danieltyukov/tud-micro-led-bonding-categorization/docs/Work with Ahmed.md

1. design of the PCB for the characterization of the led.
2. practically in the clean-room solder printing placing the led dies pick and places tool and placing it on the PCB, with the existing PCB or with the shipped new PCB from the design.
3. geometric characterization of the led dies, with 3d scans, bond line thickness and die tilt. Alignment after bonding (not expected).
4. measurement and characterization. when fully assembly.
