danieltyukov/tud-micro-led-bonding-categorization/deliverable/for_ahmed_2026-08-12/figures/daisy_chain_resistance.pdf

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
ditio

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
Total chain resistance (+)

0.2 0.3 0.4 0.5 0.6
