danieltyukov/tud-micro-led-bonding-categorization/deliverable/for_ahmed_2026-08-12/figures/daisy_chain_resistance.png

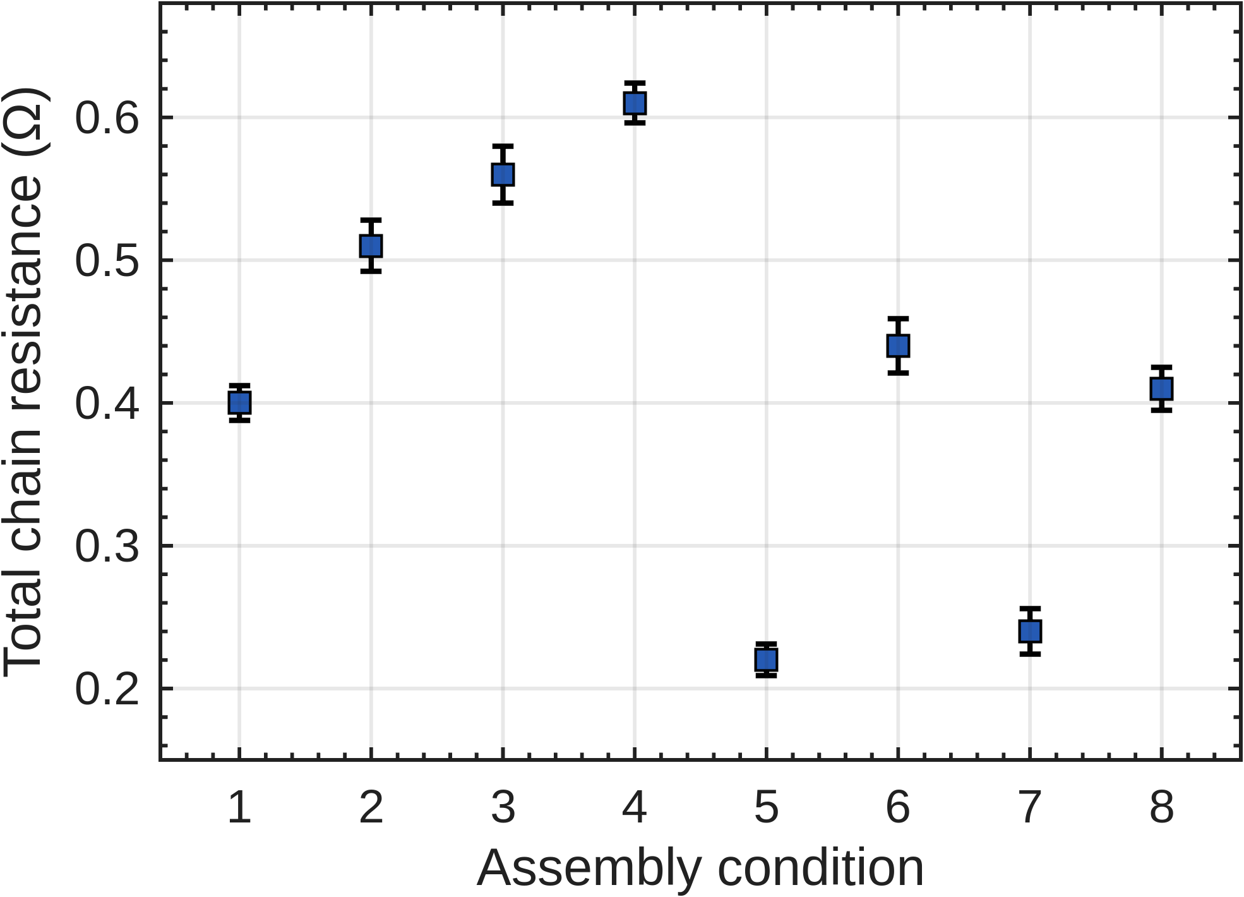
deliverable/for_ahmed_2026-08-12/figures/daisy_chain_resistance.png
