danieltyukov/tud-micro-led-bonding-categorization/deliverable/for_ahmed_2026-10-10/figures/die_shear_strength_bars.png

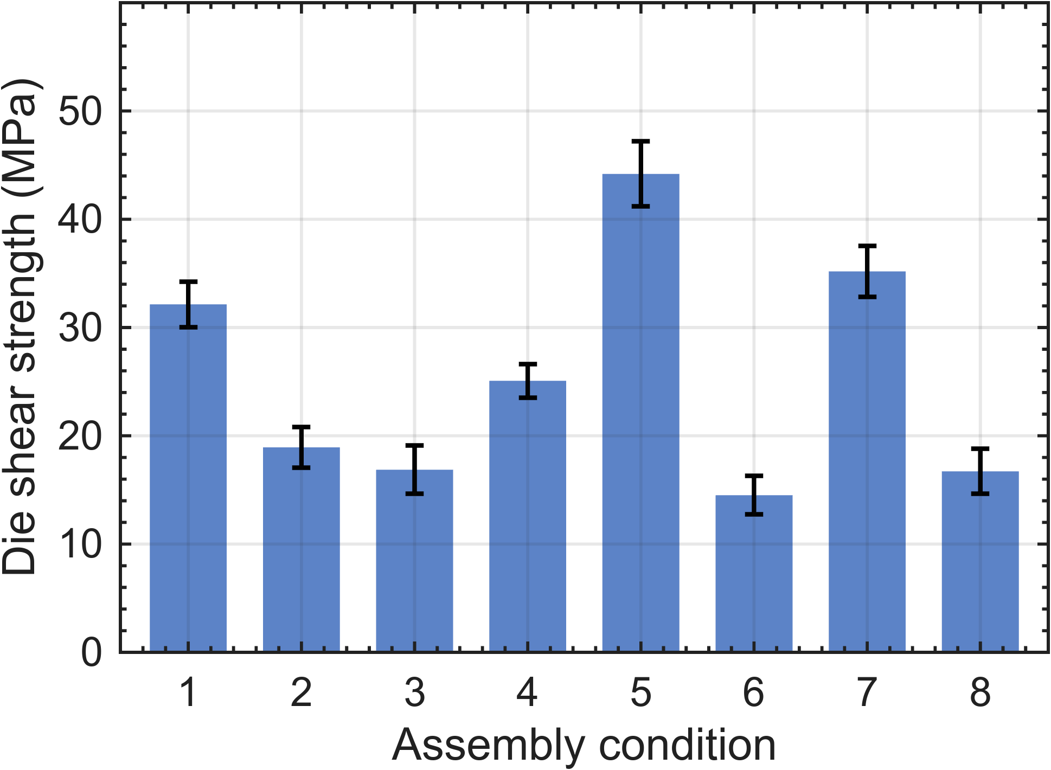
deliverable/for_ahmed_2026-10-10/figures/die_shear_strength_bars.png
