danieltyukov/tud-micro-led-bonding-categorization/new-pcb/fab/stencil-v2/paste_preview.png

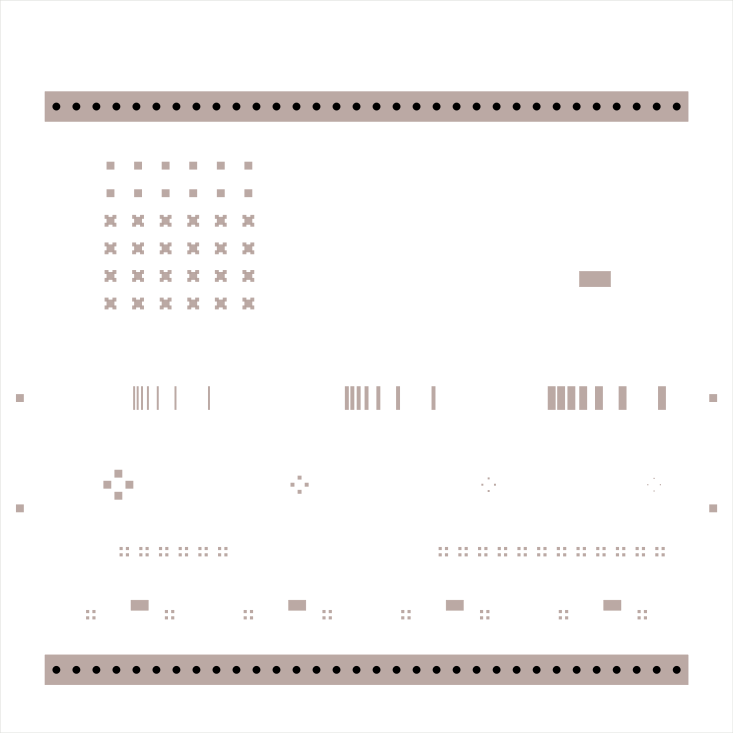
new-pcb/fab/stencil-v2/paste_preview.png
