danieltyukov/tud-micro-led-bonding-categorization/part2/photos-during-lab2/20260522_151641.jpg

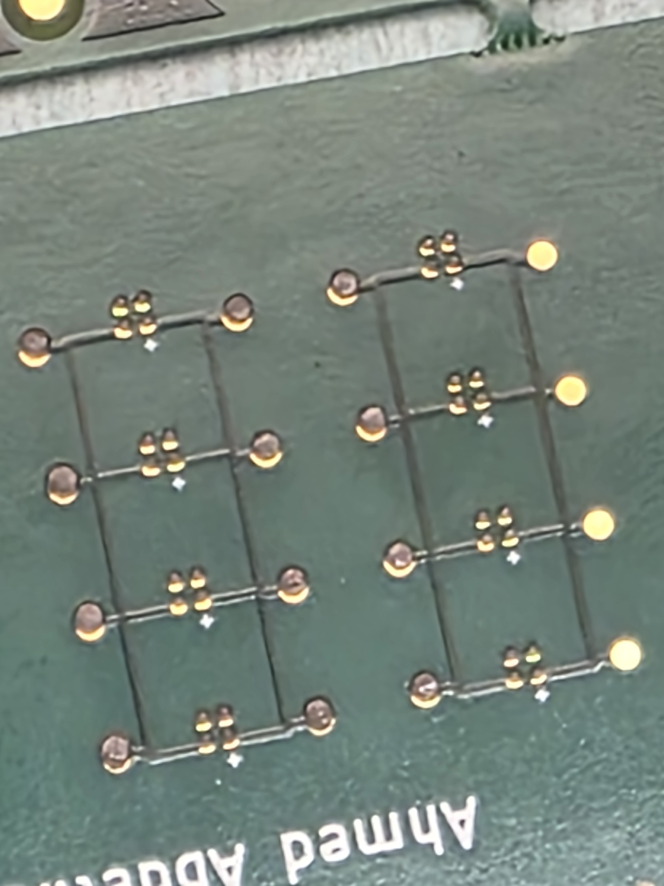
part2/photos-during-lab2/20260522_151641.jpg
