danieltyukov/tud-micro-led-bonding-categorization/part2/photos-during-lab2/20260522_152103.jpg

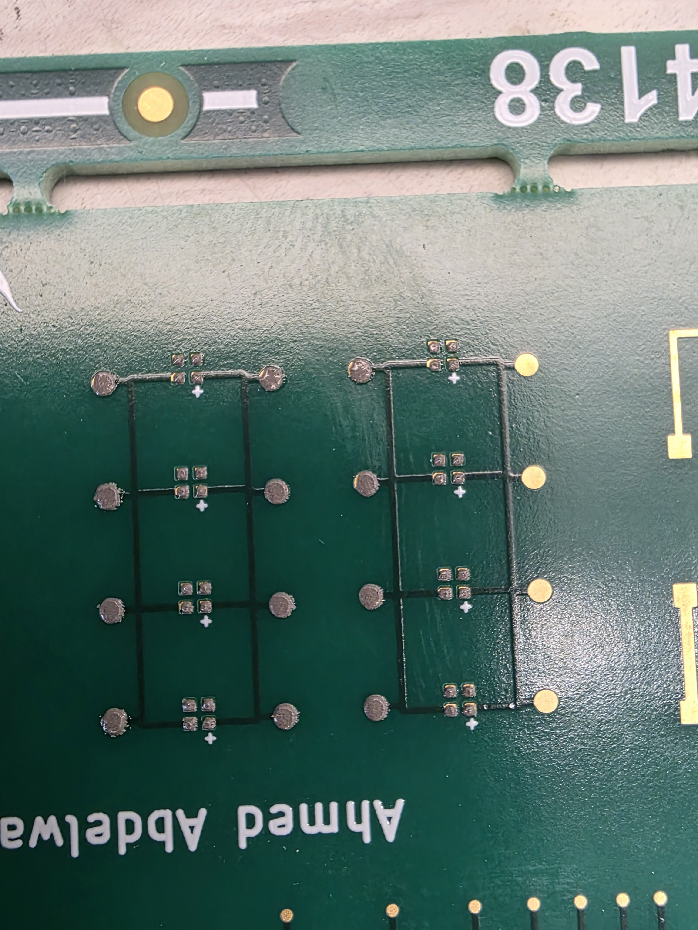
part2/photos-during-lab2/20260522_152103.jpg
