danieltyukov/tud-micro-led-bonding-categorization/report/figures/schematic.png

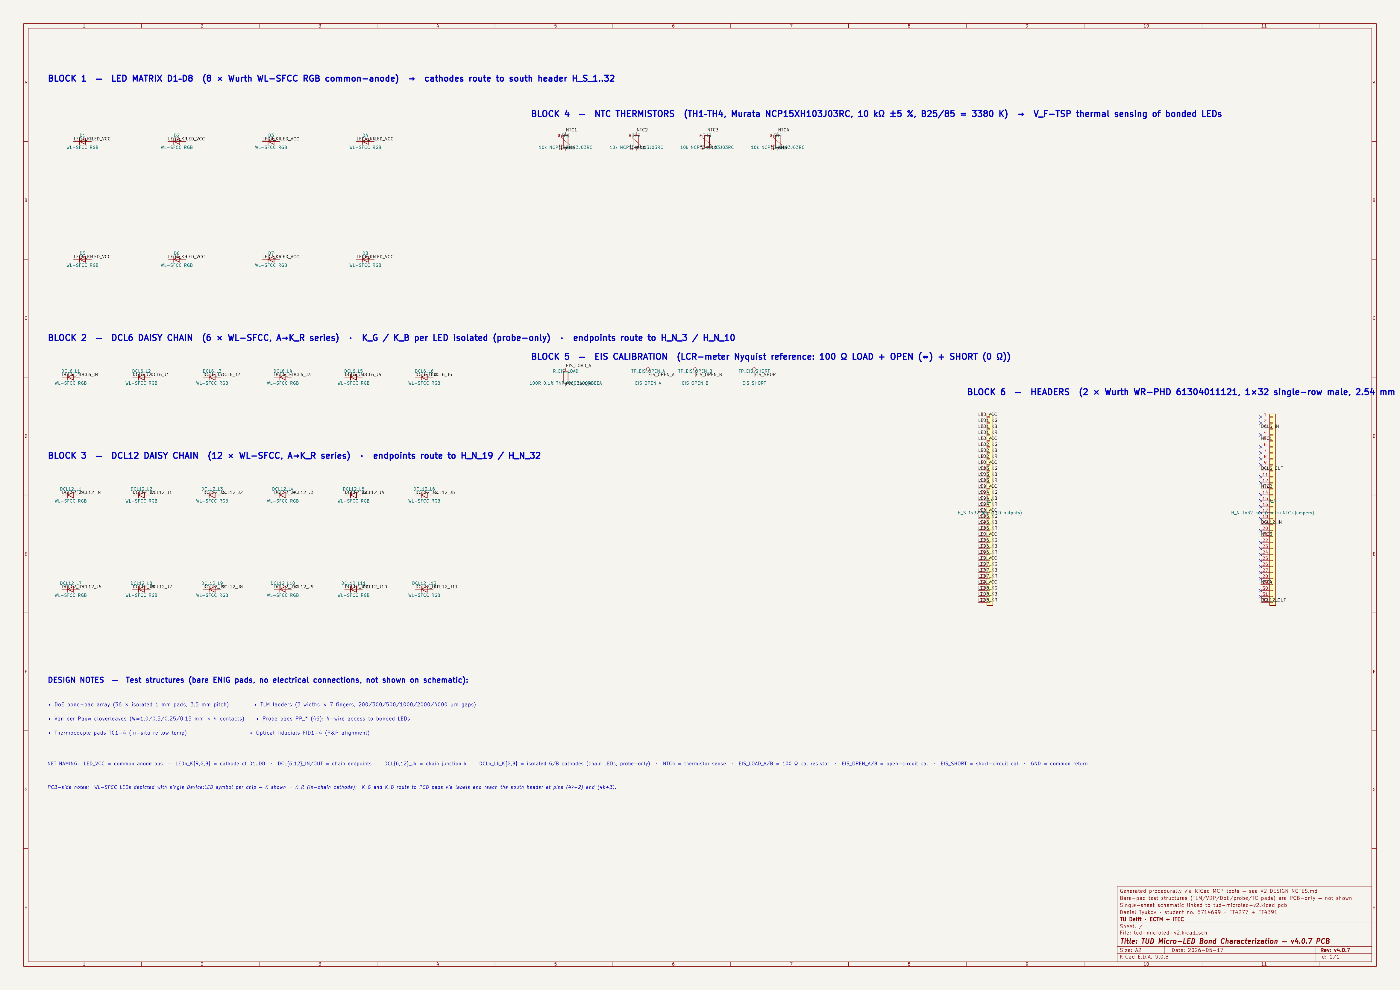
report/figures/schematic.png
