danieltyukov/tud-micro-led-bonding-categorization/RESULTS/R1_photos/2026-08-03_board1_overview.jpg

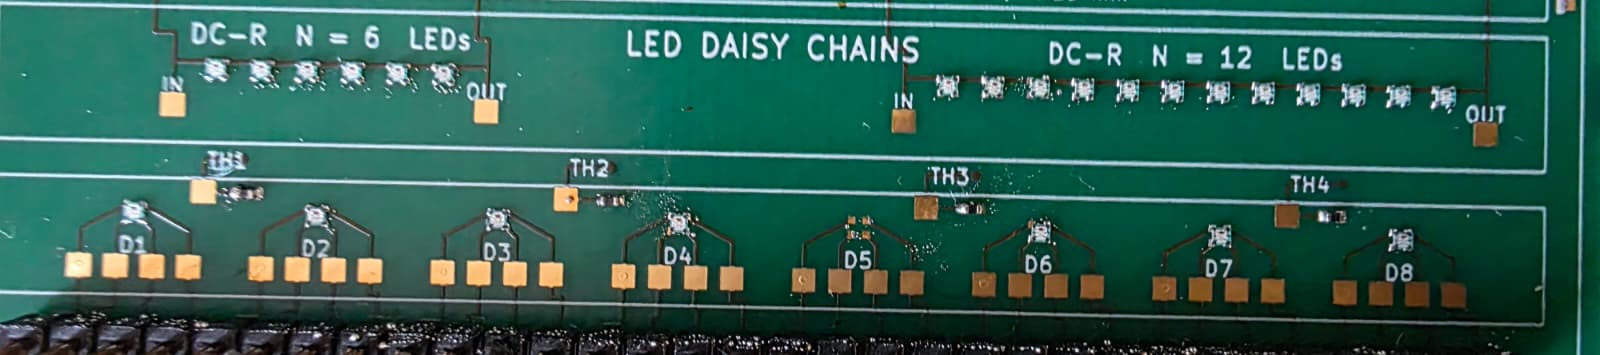
RESULTS/R1_photos/2026-08-03_board1_overview.jpg
