danieltyukov/tud-micro-led-bonding-categorization/RESULTS/R1_photos/2026-08-03_board2_overview.jpg

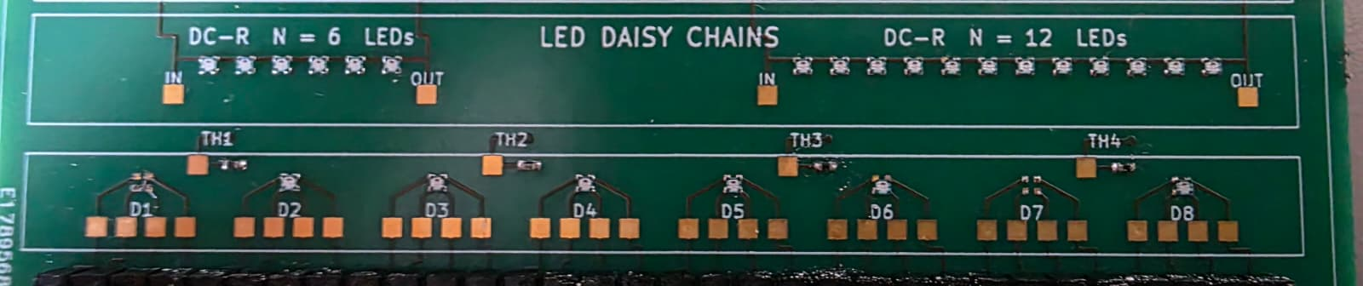
RESULTS/R1_photos/2026-08-03_board2_overview.jpg
