danieltyukov/tud-micro-led-bonding-categorization/RESULTS/R1_photos/2026-08-03_board7-8_overview.jpg

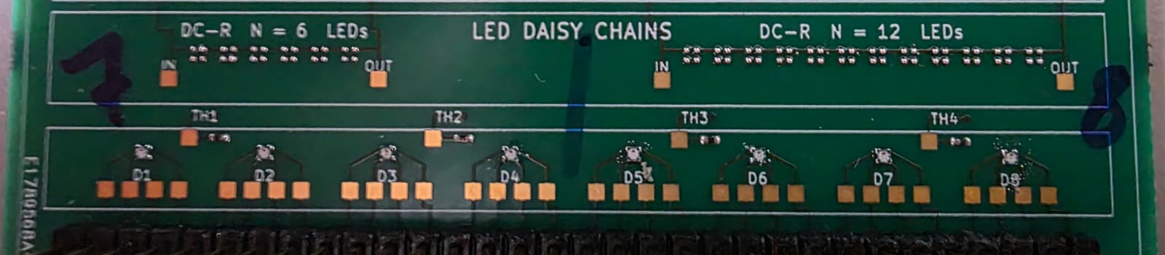
RESULTS/R1_photos/2026-08-03_board7-8_overview.jpg
