danieltyukov/tud-micro-led-bonding-categorization/deliverable/microLED_electrical_characterization/firmware/reverse_bias_wiring.pdf

Step 6 - reverse leakage. Rewire from the sweep rig.

The bank comes off, the die is driven BACKWARDS, and the meter reads ACROSS THE DIE. Healthy reads near 5 V; a shunt pulls it down.

J | J
I | I
H | H
G | G
F | F
E | E
D | D
C | C
B | B
A | A
1 | 5 | 10 | 15 | 20 | 25 | 30

top half + both top rails: leave empty rail holes: first at col 3, then five, a one-hole gap, five, ...

FORCE

GND
FORCE

GND

ATmega328P

## ARDUINO UNO

SCLSDAARFGND 13 12 11 10 9 | 8 | 7 | 6 | 5 | 4 | 3 | 2 | 1 | 0
NC IOR RST3V3 5V GNDGNDVIN | A0 A1 A2 A3 A4 A5

DIGITAL

POWER | ANALOG IN

### your PCB - SOUTH 32-pin header

pins 1-4 = D1, 5-8 = D2, ... 29-32 = D8

KR

1

A KG KB KR

5

A KG KB KR

9

A KG KB KR

13

A KG KB KR

17

A KG KB KR

21

A KG KB KR

25

A KG KB KR

29

A KG KB

32

D1 | D2 | D3 | D4 | D5 | D6 | D7 | D8
die Dn: anode = pin 4n-2 red K = 4n-3 green K = 4n-1 blue K = 4n

REMOVE these six D2-D7 jumpers - that kills the bank everything faded stays on the board, it is simply not used

100 k, measured 98.0 k

GND rail col 28

RED probe - J14

BLACK probe
any GND rail hole

the meter goes across the DIE, not across the resistor

## the rewire, in five moves

1 PULL the six jumpers off UNO D2-D7. Bank is dead.

2 ADD a jumper: UNO 5V -> G10.

3 ADD the 100 k across the top half: F10 to F14.

4 MOVE F/M #1 to G14, out to the die CATHODE.

5 MOVE F/M #2 to GND rail col 28, out to the ANODE.

## reading it

DMM on DC VOLTS, 20 V range. Not millivolts. Red probe in J14, black in any GND rail hole. Wait 5 seconds, then read the volts.

healthy die (>10 M) about 4.95 V
1 M shunt 4.50 V
100 k shunt 2.49 V
2.9 k shunt 0.14 V
Low reading = a conducting path around the junction.

## the circuit

UNO 5V

100 k

die, REVERSED

UNO GND

DMM, 20 V DC

The 100 k and the die form a divider off the 5 V rail. The die's own resistance sets the reading.
5 V reverse maximum. Never exceed it.
