danieltyukov/tud-micro-led-bonding-categorization/deliverable/microLED_electrical_characterization/firmware/rig_wiring.pdf

# Arduino I-V rig - build this

Top view, drawn hole for hole. Only the bottom half of the breadboard is used.

J | J
I | I
H | H
G | G
F | F
E | E
D | D
C | C
B | B
A | A
1 | 5 | 10 | 15 | 20 | 25 | 30

top half + both top rails: leave empty rail holes: first at col 3, then five, a one-hole gap, five, ...

FORCE

GND
FORCE

GND

ATmega328P

## ARDUINO UNO

SCLSDAARFGND 13 12 11 10 9 | 8 | 7 | 6 | 5 | 4 | 3 | 2 | 1 | 0
NC IOR RST3V3 5V GNDGNDVIN | A0 A1 A2 A3 A4 A5

DIGITAL

POWER | ANALOG IN

### your PCB - SOUTH 32-pin header

pins 1-4 = D1, 5-8 = D2, ... 29-32 = D8

KR

1

A KG KB KR

5

A KG KB KR

9

A KG KB KR

13

A KG KB KR

17

A KG KB KR

21

A KG KB KR

25

A KG KB KR

29

A KG KB

32

D1 | D2 | D3 | D4 | D5 | D6 | D7 | D8
die Dn: anode = pin 4n-2 red K = 4n-3 green K = 4n-1 blue K = 4n

D7 220 R

D6 330 R
D5 1 k

D4 2 k

D3 5.1 k
D2 10 k
RETURN | resistor bank

cols 4 + 8

C2

C3

C1

100 R sense

## build it in this order

### 1 six bank resistors: row A col 14..24, other leg FORCE one col right 2 jumper D2..D7 into row E of its own bank column 3 link E4 to E8 - all ten of those holes are now RETURN

4 100 R from B8 down to the GND rail

### 5 C2 from A4, C3 from A8 to GND rail; C1 across the rails (68 nF) 6 jumper UNO GND to the GND rail col 3 - the only ground wire 7 jumper A0 to D4, A2 to D8, A1 to FORCE col 6, A3 to GND col 10 8 two F/M jumpers out to the die you are testing

## every wire, by colour

6 x UNO D2..D7 -> row E, cols 24 22 20 18 16 14

1 x UNO GND -> GND rail, col 3

1 x UNO A0 -> RETURN, hole D4

1 x UNO A1 -> FORCE rail, col 6

1 x UNO A2 -> RETURN, hole D8

1 x UNO A3 -> GND rail, col 10 NEW

1 x link E4 - E8 (RETURN becomes one node)

F/M FORCE col 29 -> die anode, pin 4n-2

F/M RETURN, C4 -> die cathode you are testing

## check before you power up

- 12 male-male jumpers: 6 bank + A0 A1 A2 A3 + GND + 1 link
- 2 female-male jumpers - the only wires leaving the board
- 7 resistors: six in the bank, one 100 R RETURN to GND rail
- 3 caps, 68 nF each: C1 rail to rail, C2 + C3 on RETURN
- nothing in series between an ADC pin and the node it reads
- UNO GND touches the breadboard exactly once
- A0 and A2 land on the same node - that is intended
- A3 reads the GND rail: it cancels the ADC offset
- rail holes line up with the columns, starting at col 3
- each rail is one strip, so any hole on it is the same node
- the grey dash is only for boards with split rails
To change channel: move only the two female-male jumpers.

## the same thing as a circuit

D2

10 k

D3

5.1 k

D4

2 k

D5

1 k

D6

330 R

D7

220 R

FORCE | A1
C1

one die, one colour
on your PCB

F/M jumper -> pin 4n-2

F/M jumper -> cathode pin
RETURN

100 R sense

A3
UNO GND

A0

A2

C2

C3

A0 and A2 sit on the same node, so they read the same voltage.
i = (A2 - A3) / R_SENSE. The difference cancels the ADC offset.
