danieltyukov/tud-micro-led-bonding-categorization/FINAL_MEASUREMENTS/arduino-rig/leakage_step6.png

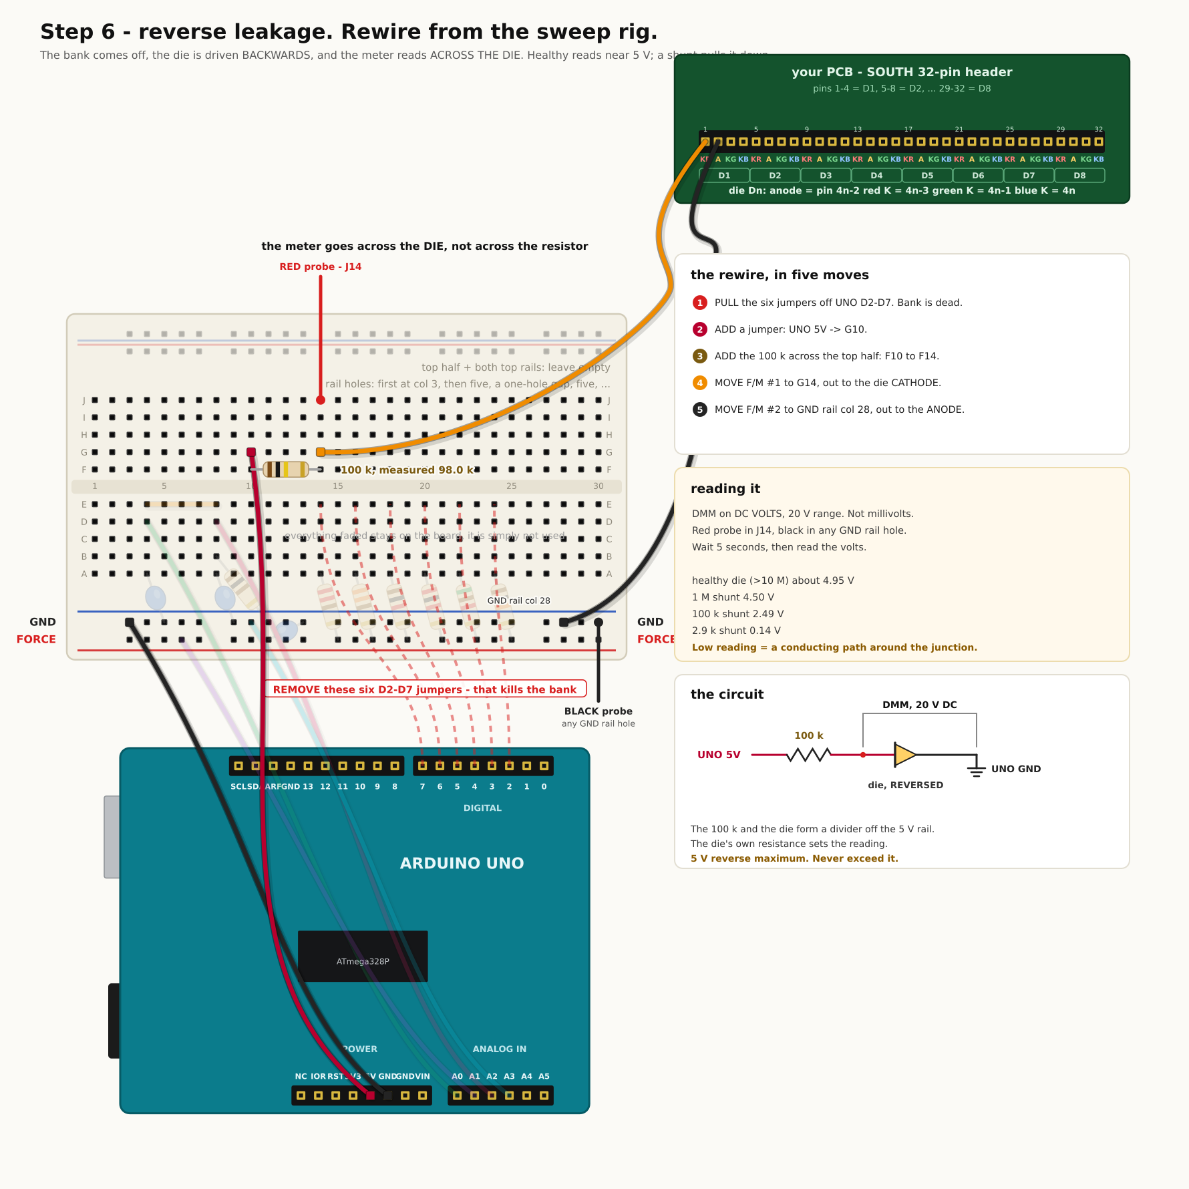
FINAL_MEASUREMENTS/arduino-rig/leakage_step6.png
