danieltyukov/tud-micro-led-bonding-categorization/measurements/DECISIONS.md

# Measurement campaign decisions

Append-only. Newest first. One entry per decision that would otherwise get re-argued.

---

## D3. Daisy chains are electrically dead: v3 must rotate the LED footprint

**Date:** 2026-08-03
**Status:** measured fact, supersedes D2

The dice sit rotated 90 deg from the KiCad footprint. Confirmed on boards 1 and 2 by
lighting each die and watching the colour. Real mapping per footprint corner:
top-left = red cathode, top-right = blue cathode, bottom-right = green cathode,
**bottom-left = anode**.

The daisy chains wire top-left to top-right on each die, intending anode to red cathode.
They therefore connect **red cathode to blue cathode**, leaving the anode floating. Each
die is two back-to-back diodes; the chain cannot conduct either way.

Confirmed by measurement: `OL` in resistance mode on all four chains, and **0 V under
illumination**, where a working 6-die chain should have produced 5-9 V photovoltaic.

### Consequences

- Both chains on both boards are unmeasurable **by any instrument**. D2's deferred battery
  stack is moot: the series path does not exist.
- The 36 chain dice remain measurable individually on their own solder fillets, anode at
  the bottom-left corner.
- **v3 fix:** correct the LED footprint's pad-to-net assignment against the Wuerth pinout
  figure. Until then any reuse of this board inherits the fault.

---

## D2. Defer driving the daisy chains end to end

**Date:** 2026-08-03
**Status:** accepted, revisit after round 1
**Scope:** the two chains on each of samples 1 and 2 (DC-A, 6 dice; DC-B, 12 dice)

### Decision

Do not attempt chain end-to-end measurement in round 1 or round 2. Removed from
`FINAL_MEASUREMENTS/1_MULTIMETER_ONLY.md` to keep that session to meter and boards only.

### Why it was deferred

The only hardware barrier is voltage: 6 dice in series need about 12 V and 12 need about
24 V. Neither the DMM nor the UNO's 5 V rail reaches that. The method needs four 9 V
batteries and clips, which were not on the table.

### What is lost

The chain is the only structure that puts all the bonds of a path in series: 12 bonds for
DC-A, 24 for DC-B. Without it, those 36 chain dice are still characterized individually
(round 1 step 7 gives each a 1 mA point, round 2 can sweep each via grabber clips), but
never as a chain.

Note the loss is modest. The measurement would be coarse anyway: chain voltage sits on the
meter's 60 V range at 10 mV per count, giving a couple of ohms of uncertainty on the chain
resistance, which spread over 12 bonds is about 0.17 Ω per bond against bonds of 0.01 to
0.1 Ω. It confirms every bond conducts and catches gross degradation. It does not resolve
normal bond variation.

### Method, if it comes back

Battery stack (+) through a series resistor into the chain **IN** pad, chain **OUT** back
to the stack (−). Two 9 V for DC-A, four for DC-B. Measure across the series resistor for
current, then across IN to OUT for chain voltage, then across the resistor again to check
drift. Five resistor values give five points: 10k / 4.7k / 2.2k / 1k / 470 for DC-A, and
22k / 10k / 4.7k / 2.2k / 1k for DC-B.

Safety point worth keeping: a reversed stack is safe **while the chain is intact**, because
the voltage divides across the dice and no single one exceeds 3 V. If one die is open it
takes the whole stack. So test polarity at the largest resistor and do not leave it
connected.

Watch the dice light as well as the meter. A dark die in an otherwise lit chain means
solder is shorting it out, which is why current still flows.

---

## D1. Do not book SMU time before the Arduino rig has run

**Date:** 2026-08-03
**Status:** accepted
**Scope:** the 8 bonded samples on the 5 v2 PCBs described in `SAMPLES.md`

### Decision

Build and run the Arduino UNO I-V rig (`ARDUINO_IV_RIG.md`) across all 120 channels
first. Do not book SMU or probe-station time for the main cross-sample comparison.

If SMU time is booked afterwards, book it **targeted**: the outliers the Arduino flags,
a golden reference subset for cross-validating the Arduino numbers, and the two chains
on samples 1 and 2. That is a half-day, not a week.

### Context

The available options were a handheld DMM (`EQUIPMENT_DMM.md`), an Arduino UNO rig built
from parts already on the bench, and a Keithley 2400-class SMU with the Summit 11K/12K
probe station recorded in `new-pcb/ELECTRICAL_CHARACTERIZATION.md:193`. Note that the
Summit is cited there as the instrument the ECTC 2025 paper used, not as confirmed TU
Delft access, so availability would have to be verified anyway.

### Rationale

**The SMU does not isolate the bond on these samples.** Every instrument measuring a
bonded LED sees

```
  R_s  =  R_die  +  R_bond_anode  +  R_bond_cathode  +  R_trace
```

R_die is of order ohms and varies die to die; the bonds are 10 - 100 mΩ. Nothing in a
Keithley removes R_die from that sum. Only a die-free structure does, and the TLM
ladders, Van der Pauw cloverleaves and DoE pads on these boards are bare ENIG with no
solder (`SAMPLES.md` section 2).

**Sample size, not resolution, is the binding constraint.** For a two-sample comparison
at α = 0.05 and 80 % power, the smallest detectable difference in mean R_s is
approximately 2.4·σ·√(2/n) at these small n. A change of Δ in mean bond resistance
appears as 2Δ in R_s, so:

| Sample | n dice | Smallest detectable bond difference |
|---|---|---|
| 3 - 8 | 4 | ≈ 1.2 × σ(R_s) |
| 1, 2 (8 individual + 18 chain) | 26 | ≈ 0.4 × σ(R_s) |

If σ(R_s) turns out to be 300 mΩ, a 50 mΩ bond difference is invisible at n = 4 with any
instrument. This is structural and no amount of instrument resolution fixes it.

**The instrument term is already far below the population term.** The Arduino rig
resolves R_s to about ±10 mΩ (1σ, from a 63-point fit). An SMU reaches about ±0.1 mΩ.
Both enter the comparison in quadrature with σ(R_s), which is expected to be hundreds of
mΩ. √(0.300² + 0.010²) = 0.3002 and √(0.300² + 0.0001²) = 0.3000. The upgrade moves
nothing.

**What the design does support well** is coarse categorization: a process that adds ohms,
produces opens, or leaves cracked joints is obvious at n = 4. That is a legitimate result
and is what "bonding categorization" reasonably means here.

### The rule that reverses this decision

After the first board's sweeps, compute the within-sample standard deviation of R_s
across its dice (`ARDUINO_IV_RIG.md` section 6.3):

- **σ ≫ 10 mΩ** (expected): the die population limits you. The SMU changes nothing for
  the comparison. Decision stands.
- **σ comparable to 10 mΩ**: the instrument limits you. Book the SMU.

This is measurable in about two hours and does not have to be guessed.

### What the SMU is still needed for

Four things, none of which is the main comparison:

1. **Pulsed measurement.** Self-heating is the dominant error and fakes roughly −1.2 Ω of
   series resistance (`ARDUINO_IV_RIG.md` section 7.1). The Arduino's shortest useful
   pulse is a few ms and can only hold the bias constant; a 2461 pulses to ~100 µs and
   removes it. This is the one genuine technical gap.
2. **The N=12 chain on samples 1 and 2**, which needs ~24 V compliance. The Arduino
   alternative is a 36 V battery stack with dividers and clamps, and a probe slip there
   destroys the ATmega.
3. **Reverse leakage below ~100 nA**, if bonding-induced die damage becomes a hypothesis.
4. **Publication credibility.** An ECTC-class reviewer expects a calibrated instrument.
   A documented Arduino rig with a 0.1 % reference-resistor check and a stated error
   budget is defensible, but it is a fight to be picked deliberately, not by default.
   The golden cross-validation subset exists to avoid having to pick it.

### Consequences

- Phase order becomes: DMM screen → Arduino sweeps → decide → targeted SMU if justified.
- The Arduino rig must produce a defensible error budget, since it may end up being the
  instrument of record. `ARDUINO_IV_RIG.md` section 7 is therefore not optional reading.
- The `R_EIS_LOAD` verification sweep at the start of every session is mandatory, since
  it is the only traceable calibration in the chain.

### Implication for a v3 board

The case for a full SMU campaign becomes strong again on a board where the bond can be
isolated from the die. Two changes would do it:

1. **Paste and reflow the TLM ladders and Van der Pauw cloverleaves**, so contact
   resistivity and sheet resistance are measurable at all.
2. **Restore dummy-die daisy chains alongside the LED chains.** Iteration 28 replaced the
   dummy-die chains with WL-SFCC LED chains (`new-pcb/V2_DESIGN_NOTES.md:154`). A metal
   dummy die has near-zero, low-variance resistance, so R_chain ≈ 2N·R_bond and the bond
   is the entire signal. With LEDs, R_die returns with all its variance and the advantage
   is lost. That swap bought optical go/no-go and cost the clean bond measurement.

3. **Put chains on every condition, and raise n per condition.** Samples 3 - 8 having only
   4 dice each is the single largest limitation of this campaign, and it is a layout and
   bonding-plan decision, not an instrument decision.
