danieltyukov/tud-micro-led-bonding-categorization/Electrical_Characterization_section.docx

[ Working note — delete before submission. ] Tables II–VIII are pre-formatted with empty cells; fill them once the cleanroom measurements are in. The first column of every measurement table is labelled “Sample / condition” so the same section serves both papers: for the molten-solder paper put the paste alloy and pad finish there (e.g. SAC305 / ENIG, TS391LT Sn42Bi57.6Ag0.4 / ENIG); for the liquid-assisted-assembly paper put the assembly medium or process variant. Symbols are real Word sub/superscripts, so they edit like normal text. Citation placeholders read “[ref]”.

# Electrical characterization

Once the micro-LEDs are bonded, each populated coupon is characterized electrically to confirm that the joints carry current and to quantify joint quality independently of the optical result. Five quantities are extracted on the same ENIG substrate and, where possible, on the same coupon: daisy-chain bond resistance and yield, the LED forward voltage and current–voltage (I–V) characteristic, the specific contact resistivity from transmission-line structures, the sheet resistance from van der Pauw cloverleaves, and the junction-to-substrate thermal resistance from forward-voltage thermometry. Impedance spectroscopy is an optional sixth measurement that resolves the joint into an equivalent circuit. All structures are contacted with four-wire (Kelvin) probes to remove lead and contact resistance from the reading. Table I lists the instruments and the structure used for each quantity.

Table I. Measurement setup: quantity, on-board test structure, instrument, and excitation.

Quantity | Test structure | Instrument | Excitation / conditions
Bond / chain resistance | Daisy chains DCL6, DCL12 (2N bonds) | Keithley 2450 SourceMeter, 4-wire | DC, I-sweep
Forward voltage & I–V | Bonded LED, four bottom contacts | Keithley 2450 SourceMeter | I = 10 mA (sense); ± sweep
Specific contact resistivity ρc | TLM ladders, W ∈ {0.25, 0.5, 1.0} mm | HP 4156 parameter analyzer | 4-point, gaps 0.2–4 mm
Sheet resistance Rsh | van der Pauw cloverleaves, W ∈ {1.0, 0.5, 0.25, 0.15} mm | HP 4156 parameter analyzer | 4-point, 90° rotation
Junction–substrate Rth | LED + NTC TH1–TH4 (interleaved) | Keithley 2450, pulsed sense | 100 µA, 1 ms, 10% duty
Series / parallel impedance | LED + EIS OPEN / SHORT / LOAD | Solartron 1260A + 1296A | 10 mV AC, 0.1 Hz–1 MHz

## A. Daisy-chain bond resistance and yield

The daisy chains DCL6 and DCL12 place 6 and 12 LEDs in series through the red cathode, so a single I–V sweep across the chain endpoints exercises 2N bonds (N LEDs, two bonds each). The mean resistance per bond follows from the measured chain resistance:

Rbond = Rchain / (2N)

A defective bond appears either as a discontinuity in the chain I–V curve or as a chain forward voltage that overshoots N × VF,nom. Yield is reported as the number of conducting bonds over the total. For reference, the v1 board reported chain resistances of 0.199–0.380 Ω across die finishes and mounting conditions [ref]; values of that order indicate well-formed joints.

Table II. Daisy-chain bond resistance and yield.

Sample / condition | Chain | N (LEDs) | Rchain (Ω) | Rbond (mΩ) | Bonds OK / total | Yield (%)
| DCL6 | 6
| DCL12 | 12
| DCL6 | 6
| DCL12 | 12

## B. Forward voltage and current–voltage characteristics

Each addressable LED is read across its four bonded contacts. The forward voltage at the 10 mA operating point, VF(10 mA), is the primary number; for WL-SFCC red the nominal value is ≈ 2.05 V [ref], so a joint that adds appreciable series resistance shows up as an elevated VF. A least-squares fit of the high-current branch gives the joint series resistance Rs, and the reverse branch at −5 V gives the leakage current Ileak, which flags damaged or contaminated dies.

Table III. Per-LED forward voltage, series resistance, and leakage. Colours: R = red, G = green, B = blue.

Sample / condition | LED ID | Colour | VF at 10 mA (V) | Rs from I–V (Ω) | Ileak at −5 V (µA) | Notes

## C. Specific contact resistivity (transmission-line method)

The TLM ladders give the sheet resistance Rsh and the specific contact resistivity ρc from the total resistance measured between successive finger pairs at known gaps d. For identical contacts of width W, length L, and transfer length LT,

Rtot(d) = (Rsh / W) · d + 2Rc

Rc = (Rsh · LT / W) · coth(L / LT)

A linear fit of Rtot versus d gives Rsh from the slope and 2Rc from the intercept; the specific contact resistivity then follows as ρc = Rc · W · LT · tanh(L / LT). The three finger widths in the ladder make the width dependence of LT directly measurable.

Table IV. TLM extraction per finger width.

Sample / condition | Width W (mm) | Rsh (Ω/sq) | 2Rc (Ω) | LT (µm) | ρc (Ω·cm²)
| 0.25
| 0.50
| 1.00

## D. Sheet resistance (van der Pauw)

Each symmetric cloverleaf gives the sheet resistance directly, with no contact-geometry correction, from the implicit van der Pauw relation

exp(−π RA / Rsh) + exp(−π RB / Rsh) = 1

where RA and RB are the transverse four-point resistances measured at 90° rotation. For RA ≈ RB ≡ R this collapses to Rsh = (π / ln 2) · R. The cloverleaves cross-check the TLM slope and surface any width-dependent edge effects. The v1 board reported an effective sheet resistivity of 2.94 × 10⁻⁵ Ω·m for the ENIG pads [ref], a useful sanity check on the new readings.

Table V. van der Pauw sheet resistance per cloverleaf.

Sample / condition | Cloverleaf W (mm) | RA (Ω) | RB (Ω) | Rsh (Ω/sq) | ρsheet (Ω·m)
| 1.00
| 0.50
| 0.25
| 0.15

## E. Junction-to-substrate thermal resistance (forward-voltage thermometry)

The LED forward voltage at a fixed low sense current falls almost linearly with junction temperature, so the diode is its own thermometer. With the temperature-sensitive parameter S ≡ −∂VF/∂TJ calibrated once,

TJ(t) = TJ,0 − (1/S) · [ VF(t) − VF,0 ]

The substrate temperature is read from the interleaved NTCs (TH1–TH4) through the Steinhart-B relation 1/T = 1/T0 + (1/B) · ln(R/R0), with T0 = 298.15 K and R0 = 10 kΩ. To suppress self-heating bias the sense current is pulsed (100 µA, 1 ms, 10% duty). The bond-joint thermal resistance is the steady-state ratio of the junction-to-substrate temperature difference to the dissipated power:

Rth,bond = [ TJ(∞) − TNTC(∞) ] / Pop

Table VI. Forward-voltage thermometry: calibrated slope and extracted junction-to-substrate thermal resistance.

Sample / condition | LED ID | S = −∂VF/∂TJ (mV/K) | Pop (mW) | ΔT (K) | Rth,bond (K/W)

## F. Impedance spectroscopy (optional)

Sweeping a 10 mV AC excitation from 0.1 Hz to 1 MHz and recording the complex impedance Z(jω) = Z′ + jZ″ separates the series bond resistance (the high-frequency intercept, Z′ → Rs as ω → ∞) from the diode’s parallel RC dynamics. For the standard LED equivalent circuit (Rs in series with Rp ∥ Cj),

Z(jω) = Rs + Rp / (1 + jω Rp Cj)

The on-board EIS OPEN, SHORT, and LOAD references (the 100 Ω 0.1% resistor) calibrate the fixture before the LED is measured.

Table VII. EIS equivalent-circuit parameters.

Sample / condition | LED ID | Rs (Ω) | Rp (Ω) | Cj (nF) | fpeak (kHz)

## G. Summary of electrical results

Table VIII collects the headline number from each method into a single per-condition comparison. Cross-condition variance is the figure of merit: it captures how wide each assembly process window actually is.

Table VIII. Summary of electrical characterization across assembly conditions (one row per condition).

Condition | Yield (%) | Mean Rbond (mΩ) | VF at 10 mA (V) | ρc (Ω·cm²) | Rsh (Ω/sq) | Rth,bond (K/W)
