danieltyukov/tud-micro-led-bonding-categorization/FINAL_MEASUREMENTS/analysis/figures/fig2_defect_map.pdf

Die position

D1 D2 D3 D4 D5 D6 D7 D8

# Assembly condition S1

S2

S3

S4

S5

S6

S7

S8

pass
suspect

cross-lit
open

short
detached
