danieltyukov/tud-micro-led-bonding-categorization/FINAL_MEASUREMENTS/analysis/figures/fig3_yield_modes.pdf

20/24 14/24 3/12 8/12 12/12 9/12 12/12 10/12

Assembly condition

1 | 2 | 3 | 4 | 5 | 6 | 7 | 8

Channels (%)

0

25

50

75

100

pass
suspect

cross-lit
open

short
detached
