danieltyukov/tud-micro-led-bonding-categorization/RESULTS/daisy_chain/Total daisy chain resistance (8 conditions).xlsx

Assembly Condition | Total chain resistance (mean) | Deviation
1 | 0.4 | 0.012
2 | 0.51 | 0.018
3 | 0.56 | 0.02
4 | 0.61 | 0.014
5 | 0.22 | 0.011
6 | 0.44 | 0.019
7 | 0.24 | 0.016
8 | 0.41 | 0.015
