danieltyukov/tud-micro-led-bonding-categorization/RESULTS/die_shear/die shear strength MPa.xlsx

Assembly Condition | Die-shear Strength (Mpa) | Deviation
1 | 32.14 | 2.10
2 | 18.93 | 1.87
3 | 16.87 | 2.23
4 | 25.08 | 1.56
5 | 44.19 | 3.02
6 | 14.51 | 1.77
7 | 35.18 | 2.35
8 | 16.72 | 2.08
