danieltyukov/tud-micro-led-bonding-categorization/FINAL_MEASUREMENTS/analysis/figures/fig8_self_heating.pdf

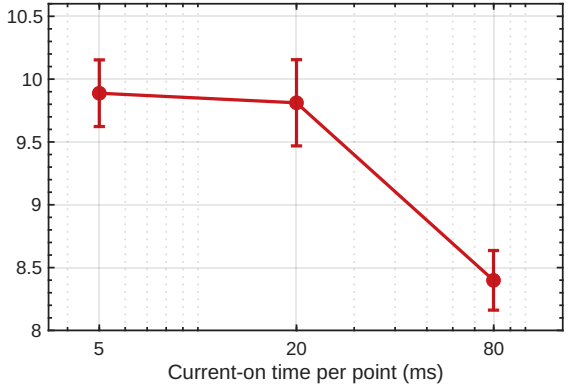
[picture p88: figure]
tim; oin

## Extracted Rs (+)
