danieltyukov/tud-micro-led-bonding-categorization/deliverable/microLED_electrical_characterization/figures/fig8_self_heating.pdf

tim; oin

## Extracted Rs (+)
