danieltyukov/tud-micro-led-bonding-categorization/FINAL_MEASUREMENTS/arduino-rig/closeup.png

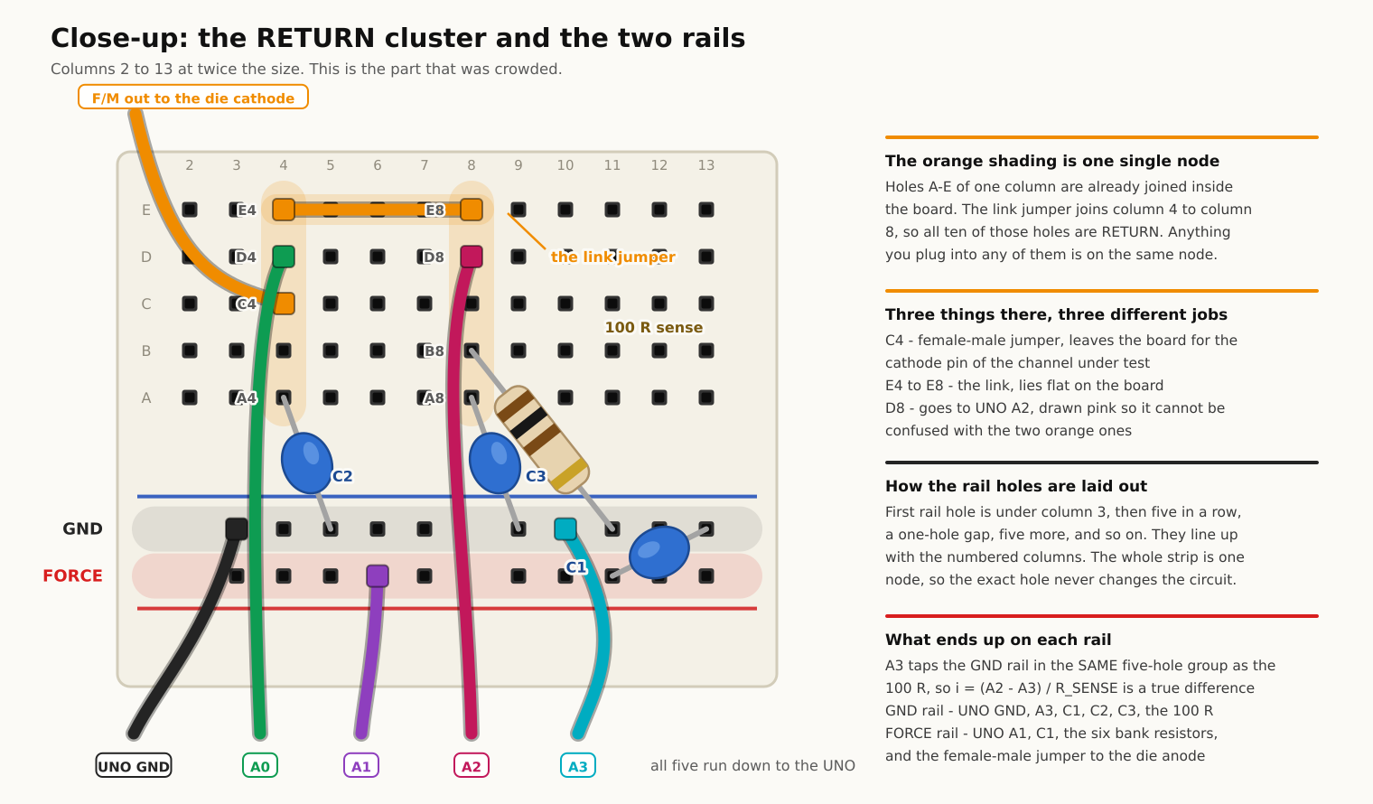
FINAL_MEASUREMENTS/arduino-rig/closeup.png
