danieltyukov/tud-micro-led-bonding-categorization/FINAL_MEASUREMENTS/board-probe-map.png

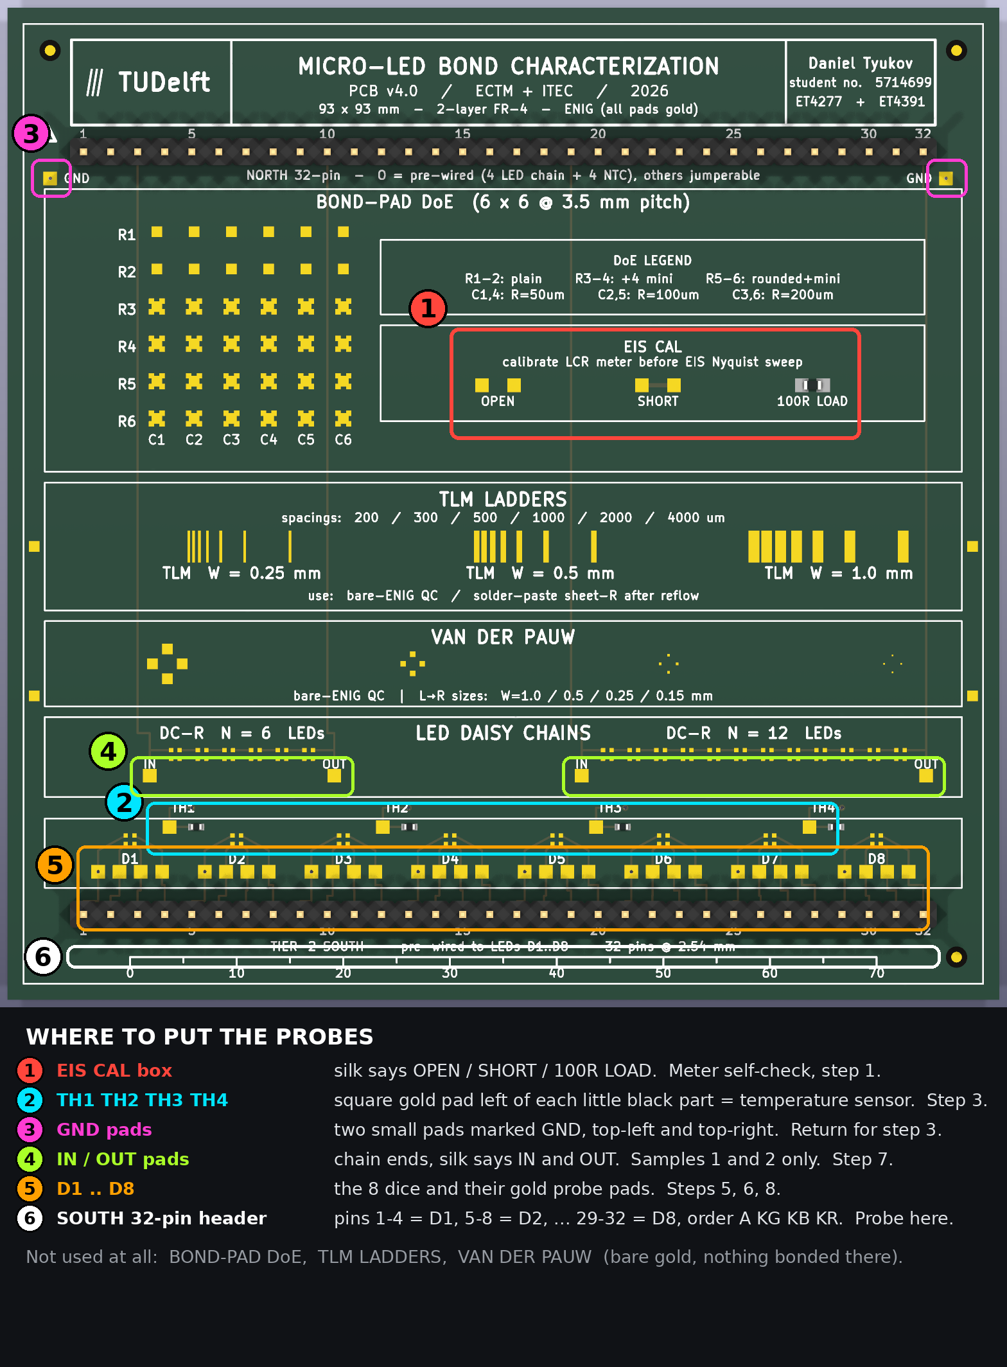
FINAL_MEASUREMENTS/board-probe-map.png
