danieltyukov/tud-micro-led-bonding-categorization/measurements/photos/2026-08-03_microcontrollers.jpg

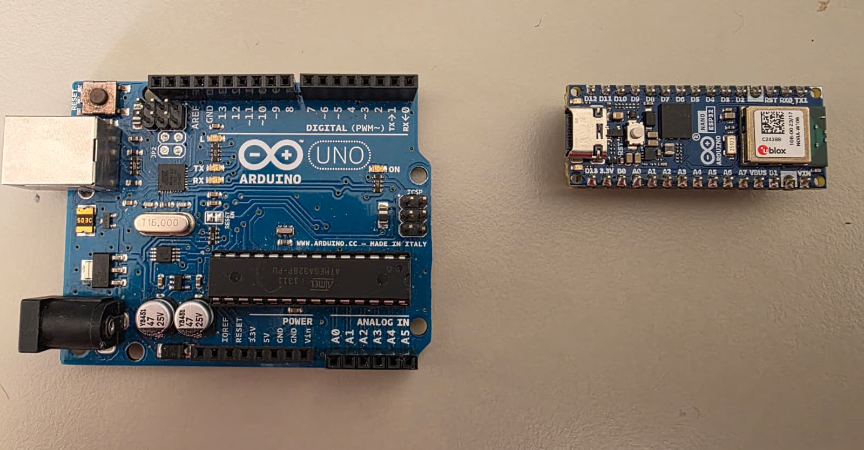
measurements/photos/2026-08-03_microcontrollers.jpg
