danieltyukov/tud-micro-led-bonding-categorization/new-pcb/fab/tud-microled-v2-schematic.pdf

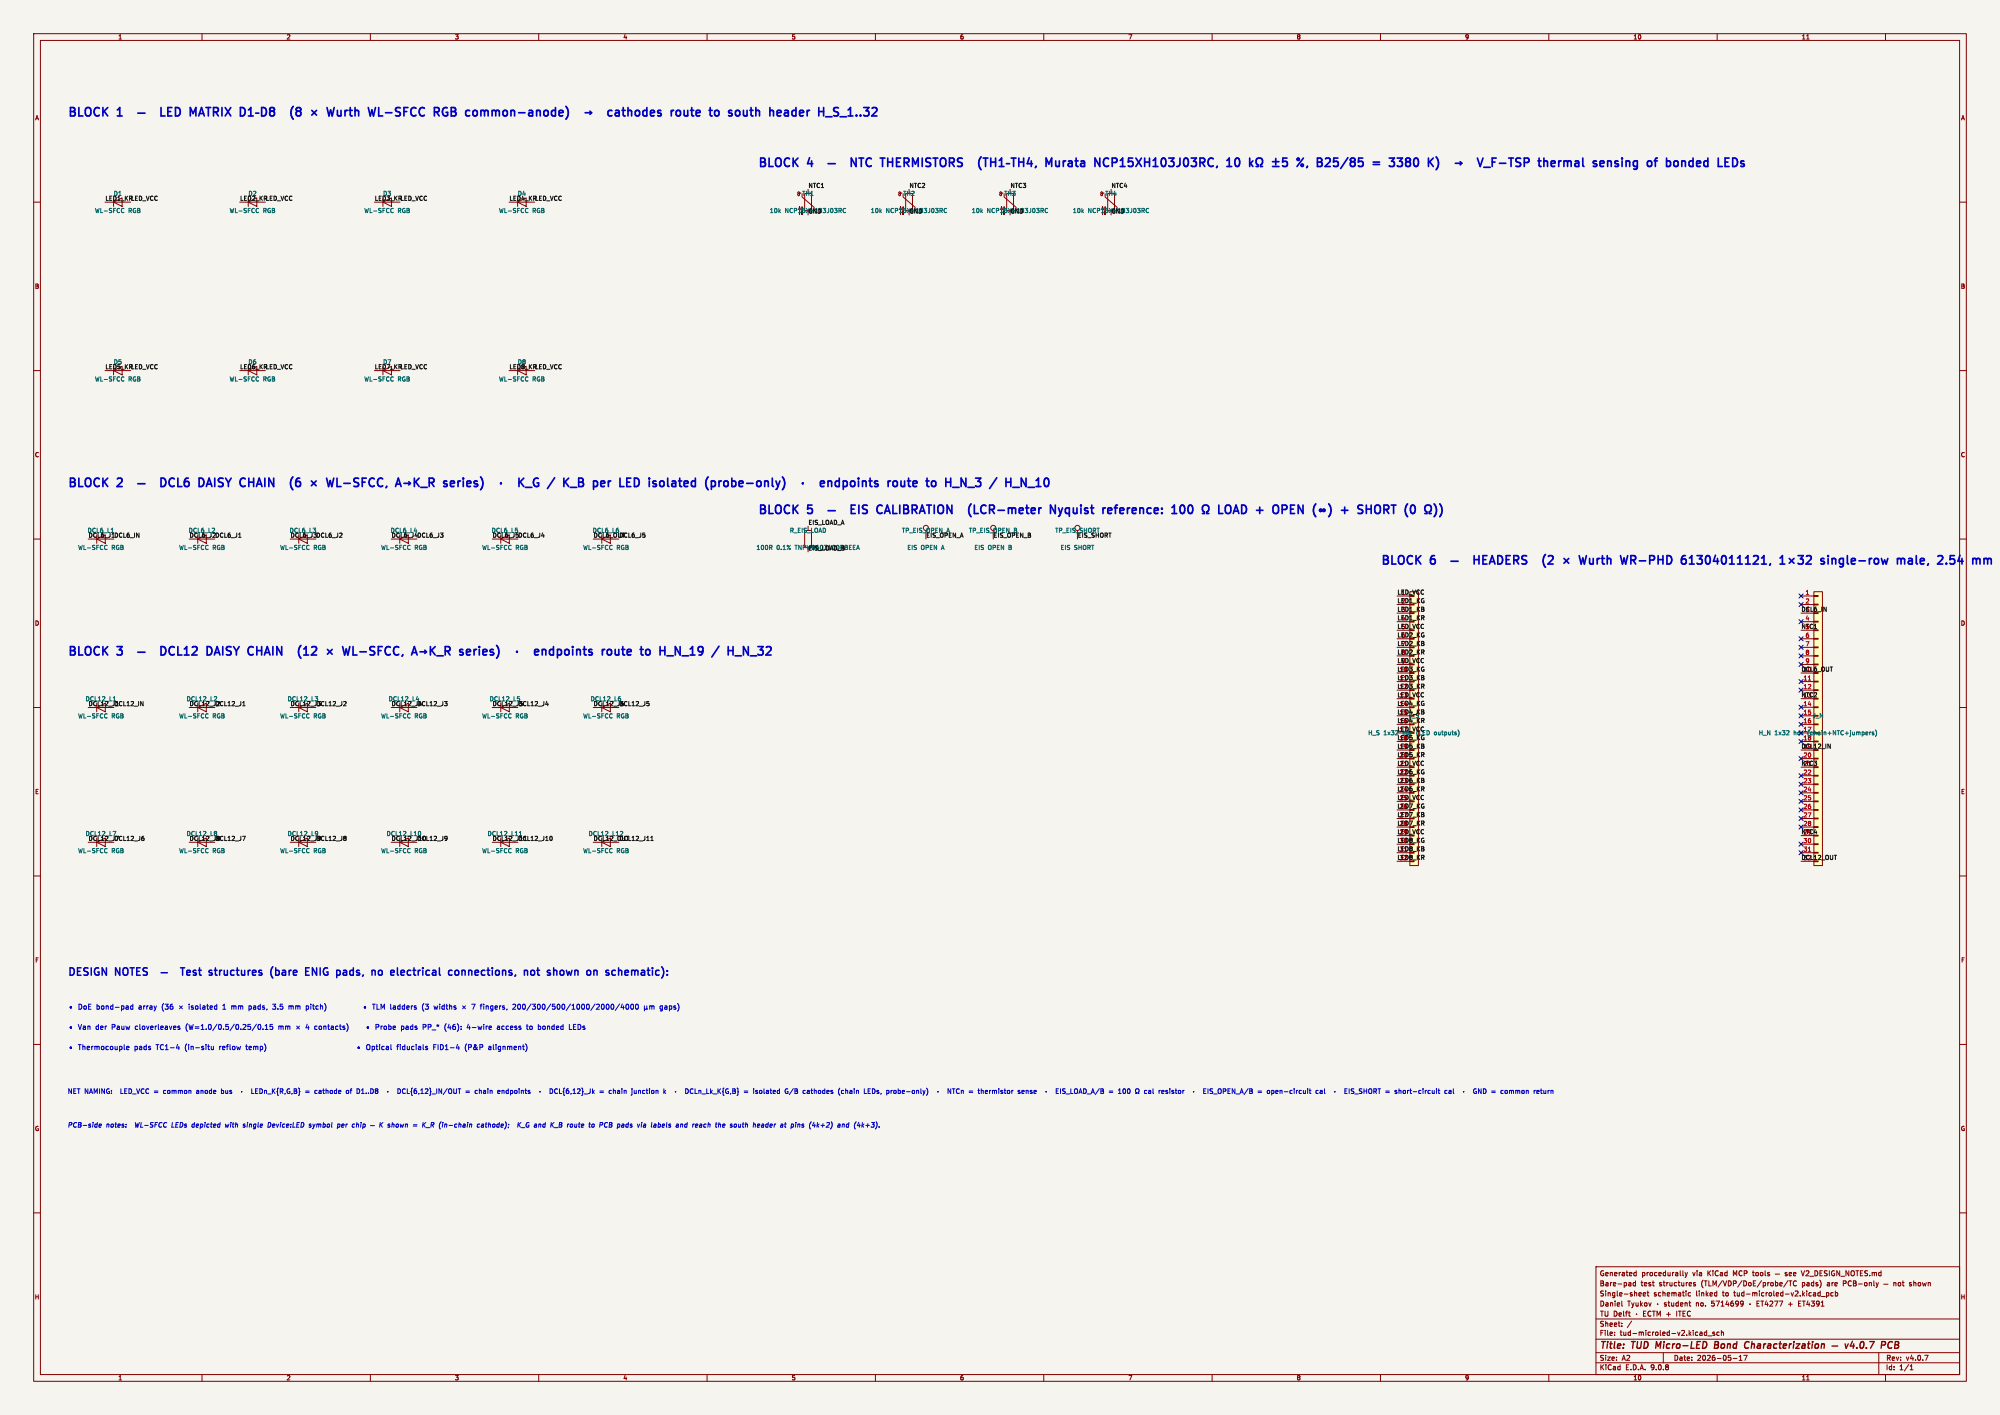
[picture p93: page 1]

D2 WL-SFCC RGB D1 WL-SFCC RGB
LED1_KR

D8 WL-SFCC RGB D4 WL-SFCC RGB

DCL12_L6 WL-SFCC RGB DCL12_L5 WL-SFCC RGB
