danieltyukov/tud-micro-led-bonding-categorization/FINAL_MEASUREMENTS/analysis/figures/fig1_iv_curves.pdf

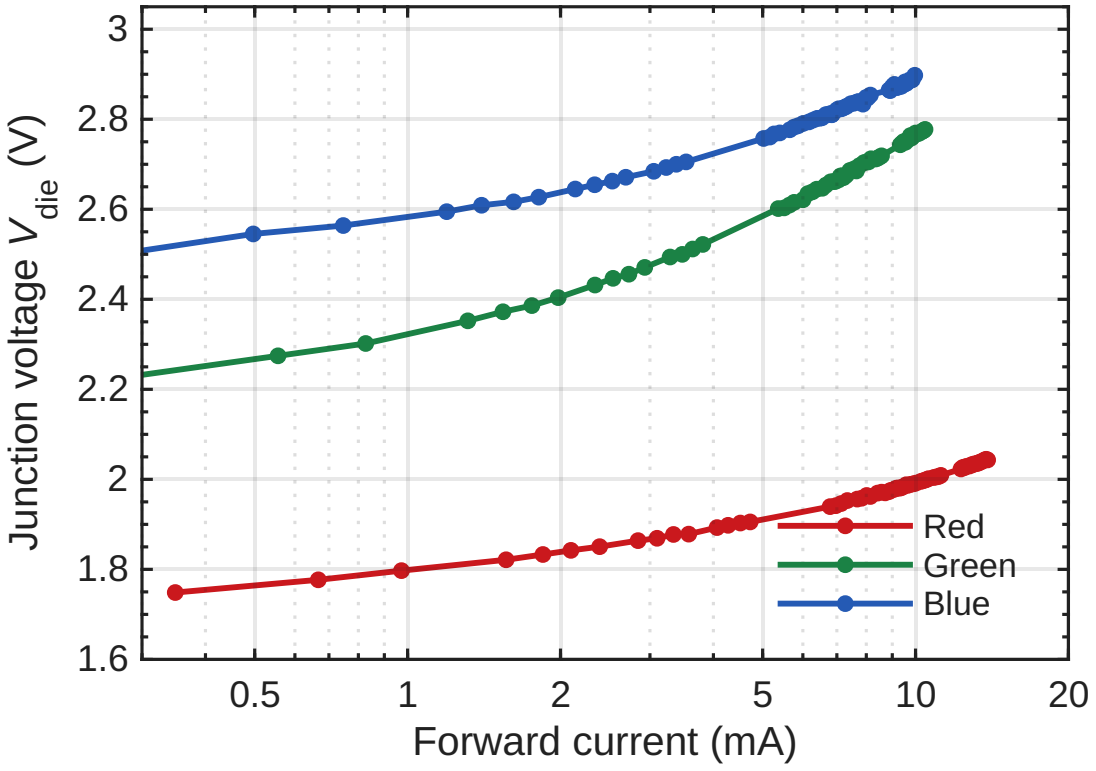
[picture p94: page 1]

Junction voltage Vdie (V)

Blu e
