danieltyukov/tud-micro-led-bonding-categorization/FINAL_MEASUREMENTS/analysis/figures/fig6_vf_by_condition.pdf

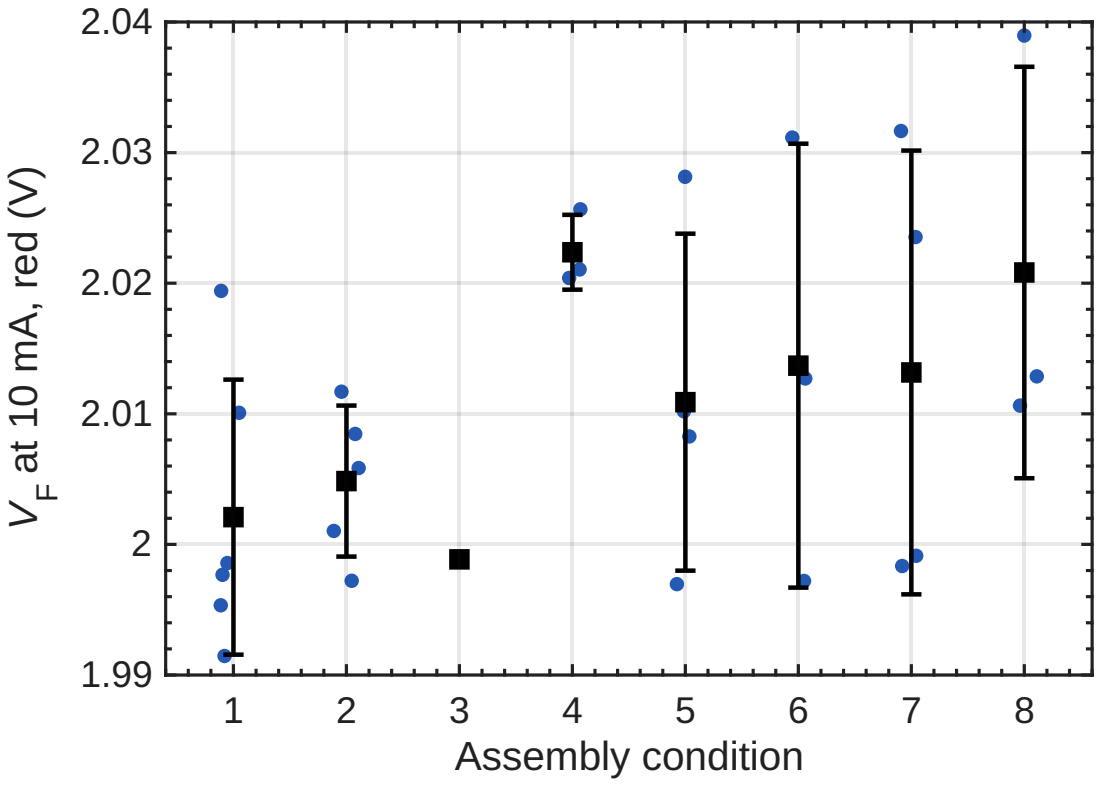
[picture p95: page 1]
bly; ditio

VF at 10 mA, red (V)
