danieltyukov/tud-micro-led-bonding-categorization/FINAL_MEASUREMENTS/analysis/figures/fig7_shunt_detection.pdf

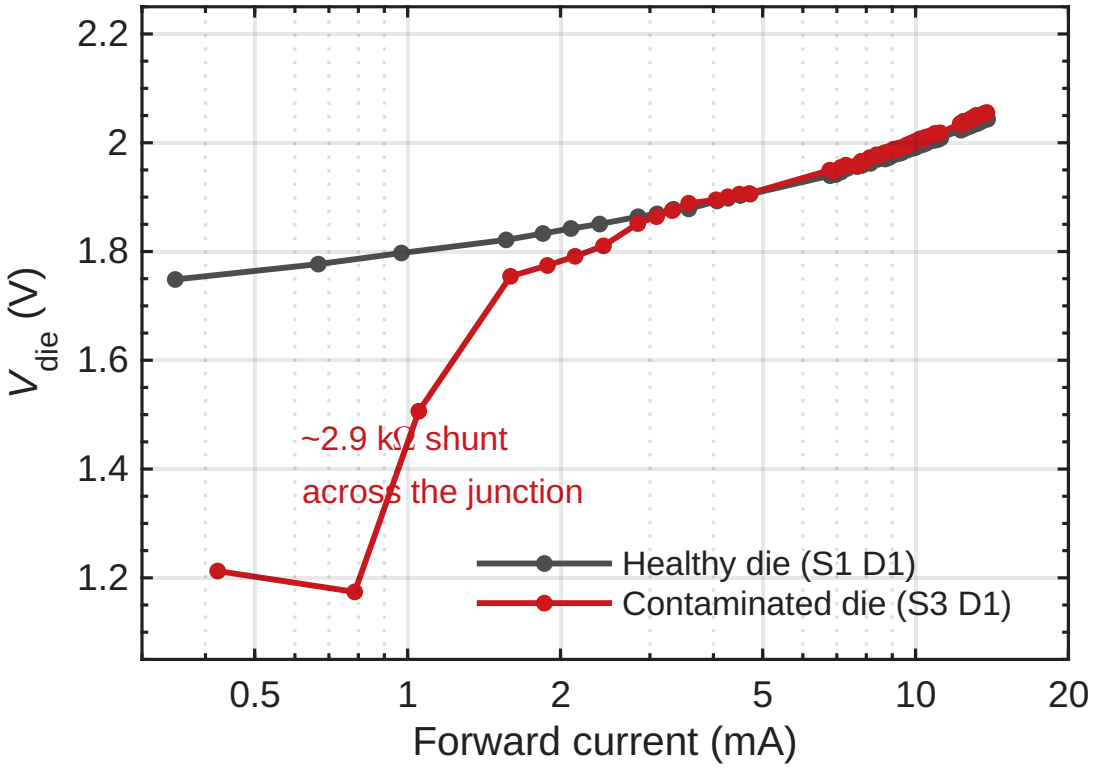
[picture p96: page 1]
Vdie

~2.9 k+ shunt
across the junction | Healthy die (S1 D1)

Contaminated die (S3 D1)

Forward current (mA)
