danieltyukov/tud-micro-led-bonding-categorization/deliverable/microLED_electrical_characterization/figures/fig1_iv_curves.pdf

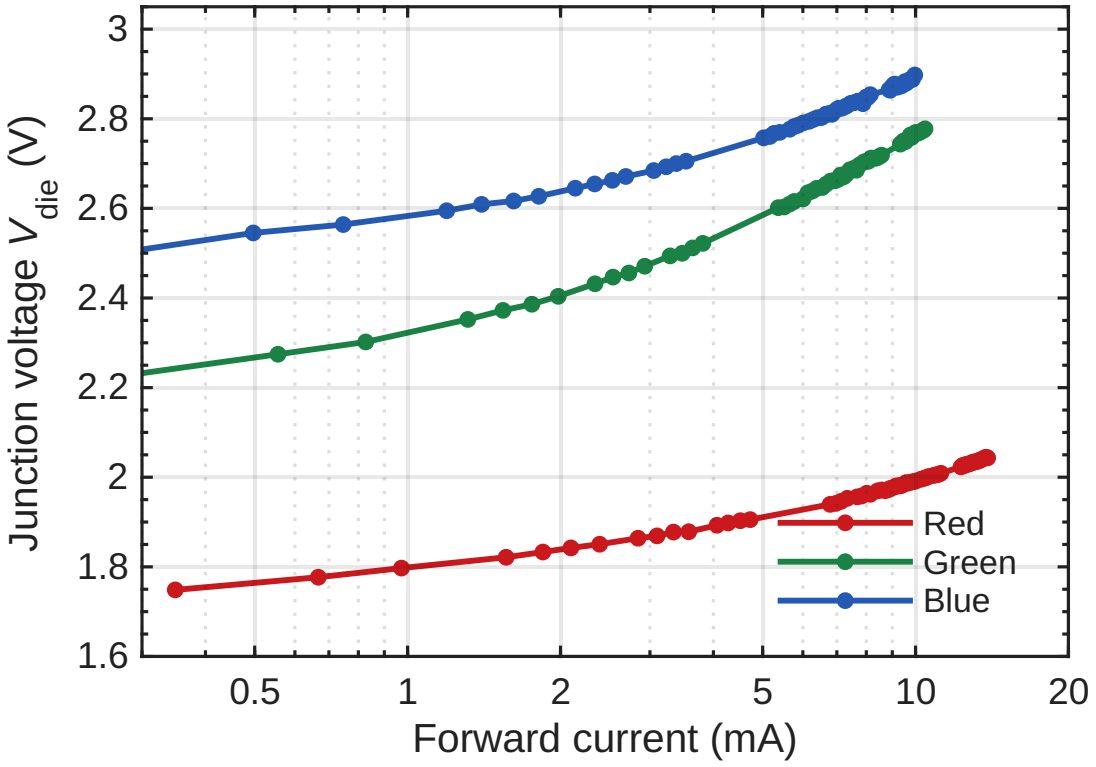
[picture p97: page 1]

Junction voltage Vdie (V)

Blu e
