danieltyukov/tud-micro-led-bonding-categorization/deliverable/microLED_electrical_characterization/figures/fig4_rs_by_condition.pdf

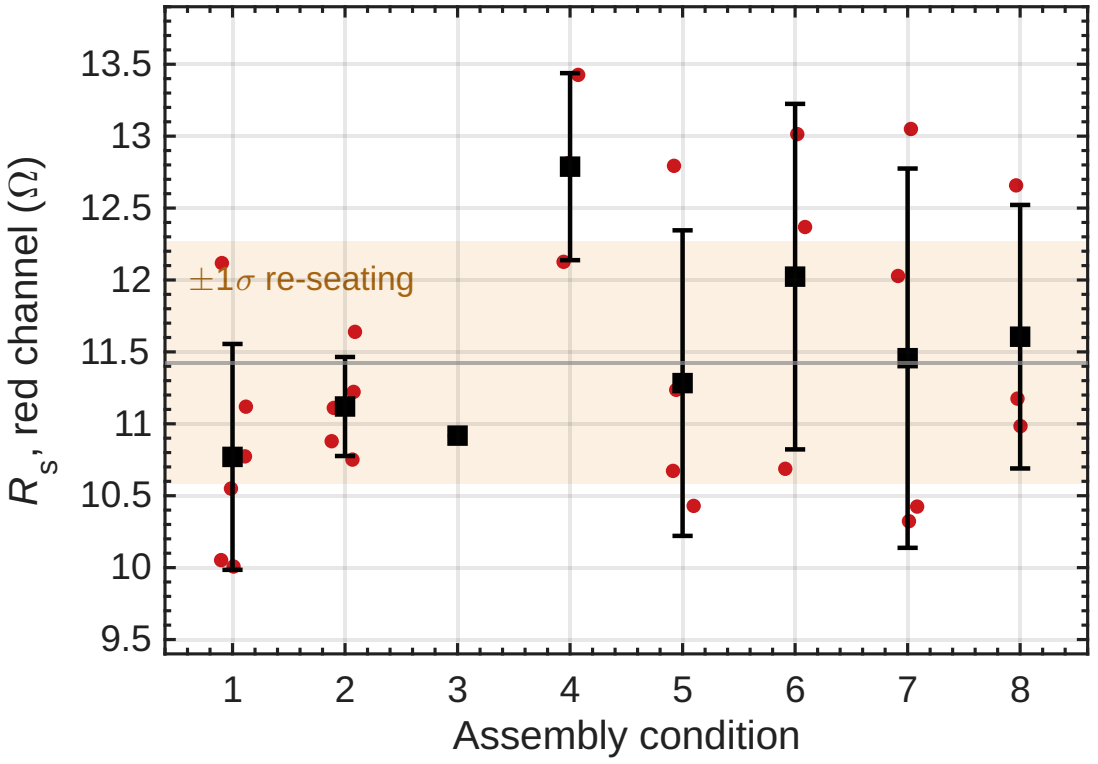
[picture p98: page 1]
'1< re-seating; Assembly condition; , red channel (+)
