danieltyukov/tud-micro-led-bonding-categorization/deliverable/microLED_electrical_characterization/figures/fig6_vf_by_condition.pdf

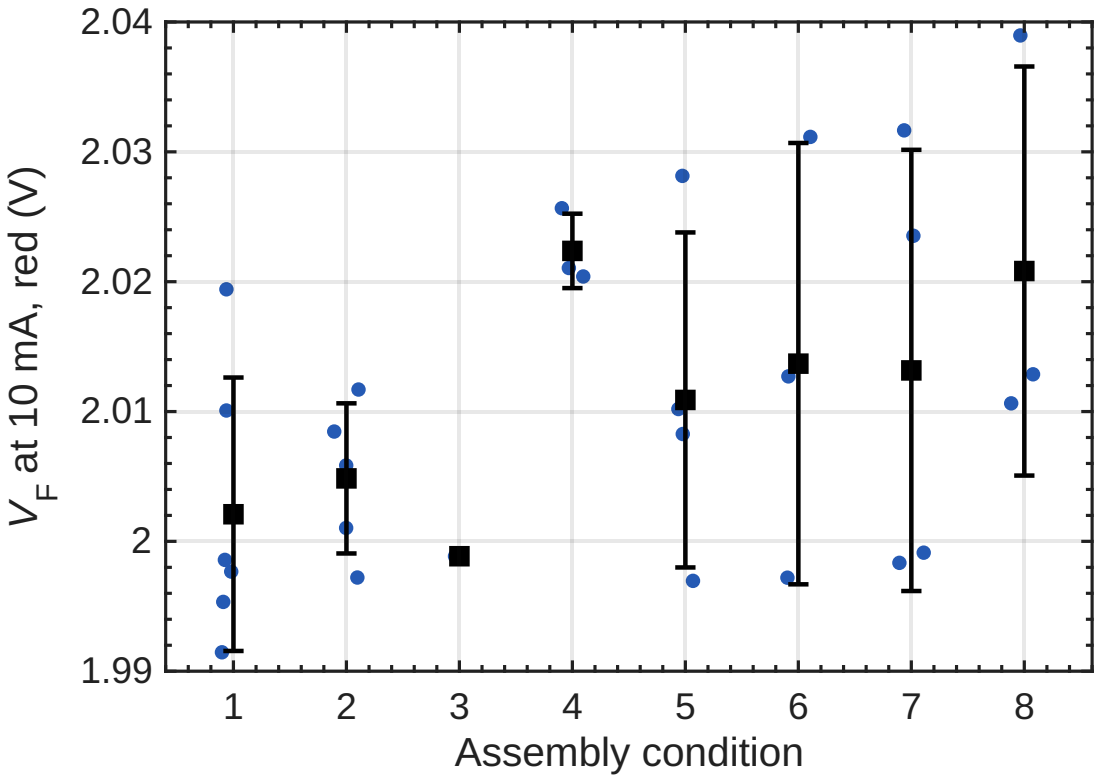
[picture p99: page 1]
bly; ditio

VF at 10 mA, red (V)
