danieltyukov/tud-micro-led-bonding-categorization/new-pcb/fab/tud-microled-v2-top.pdf

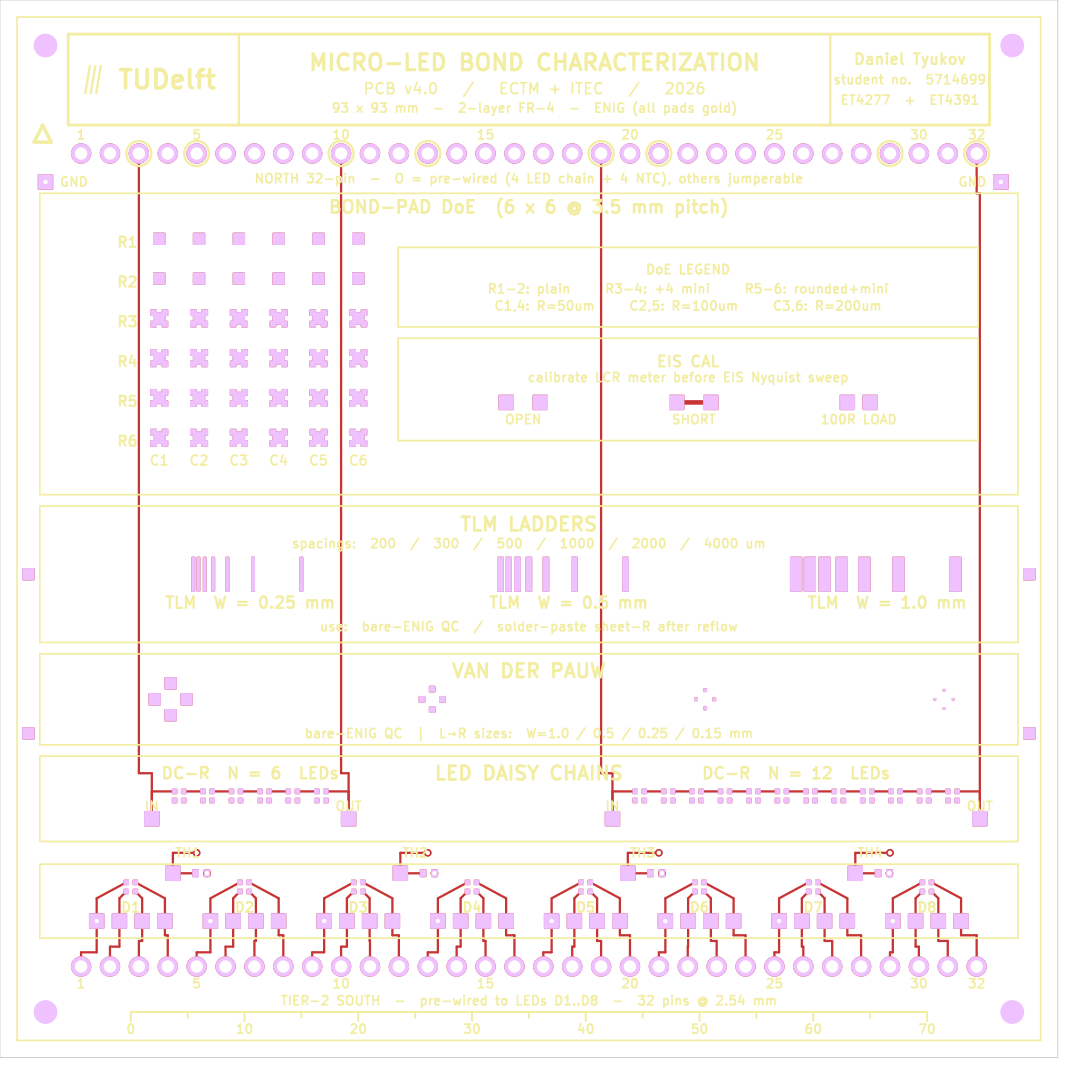
[picture p100: page 1]

spacings: | use: | 200 / 300 bare-ENIG QC / | / 500 solder-paste | / | 1000 | / 2000 / 4000 um sheet-R after reflow

DC-R N = 6 LEDs bare-ENIG | TLM W = VAN DER PAUW QC | þÿL!’Rsizes: W=1.0 | 0.5 mm DC-R N = 12 W = 1.0 mm LEDs TLM / 0.5 / 0.25 / 0.15 mm
