danieltyukov/tud-micro-led-bonding-categorization/FINAL_MEASUREMENTS/analysis/figures/fig4_rs_by_condition.pdf

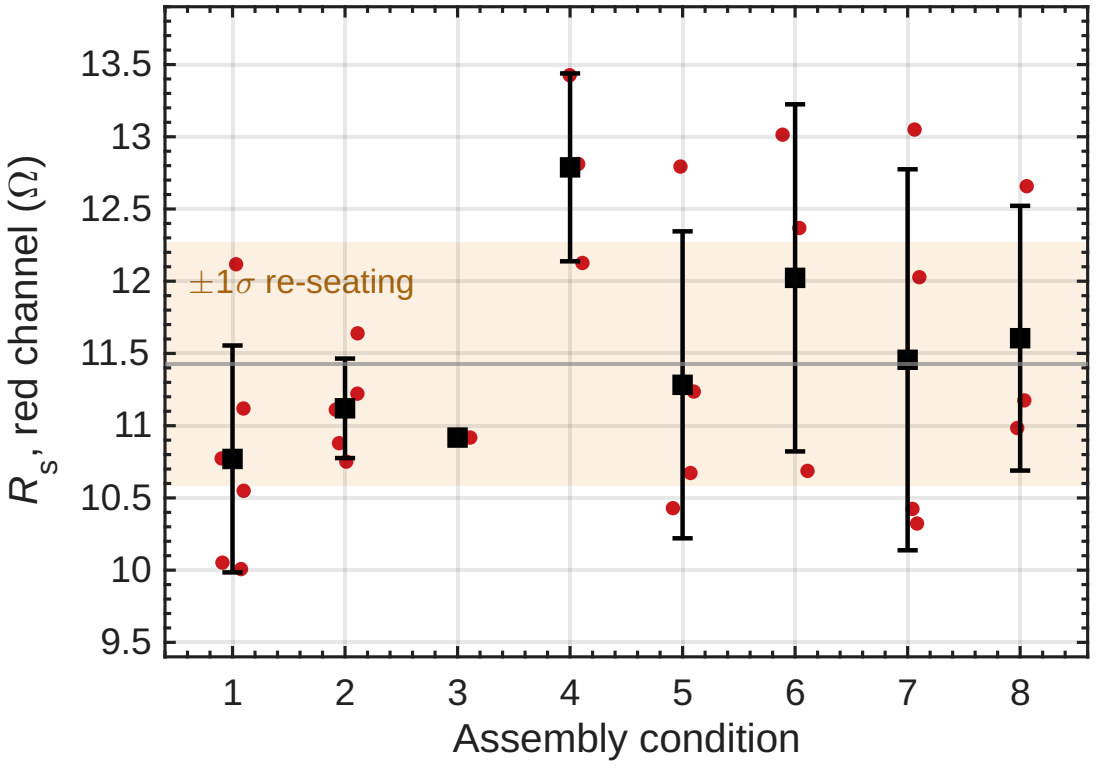
[picture p101: page 1]
bly; ditio; s, red channel (+)

1 | r e -s e | a tin g
