danieltyukov/tud-micro-led-bonding-categorization/FINAL_MEASUREMENTS/analysis/figures/fig5_reseat_repeatability.pdf

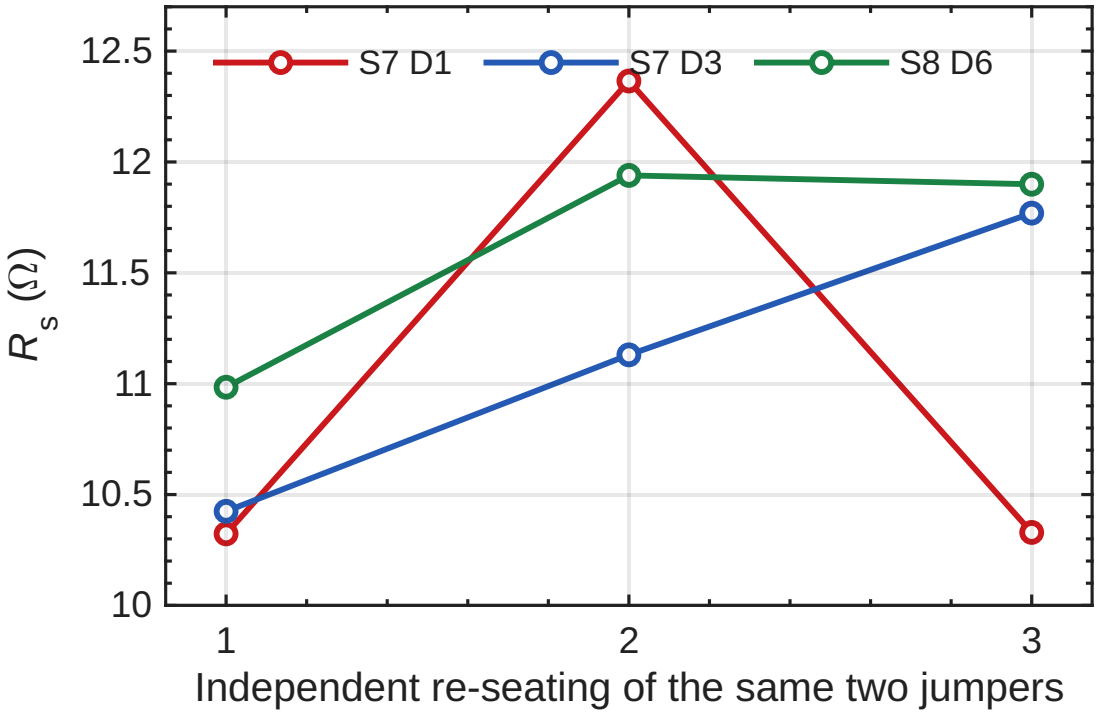
[picture p102: page 1]

Independent re-seating of the same two jumpers
