danieltyukov/tud-micro-led-bonding-categorization/deliverable/microLED_electrical_characterization/figures/fig5_reseat_repeatability.pdf

Independent re-seating of the same two jumpers
