danieltyukov/tud-micro-led-bonding-categorization/new-pcb/fab/tud-microled-v2-bot.pdf

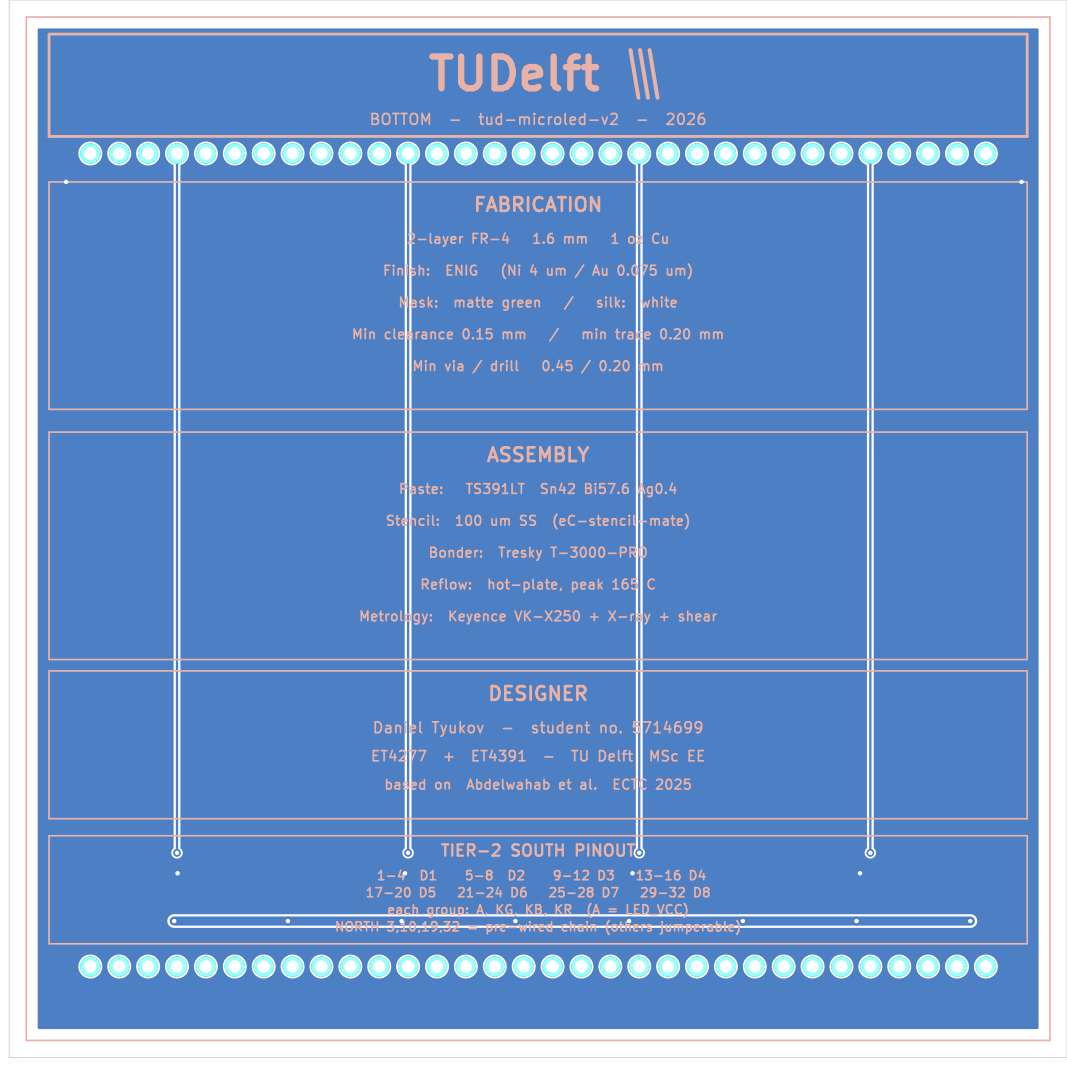
[picture p103: page 1]
